piotr-go/DIY-A586/v1.9/3D/panel.png

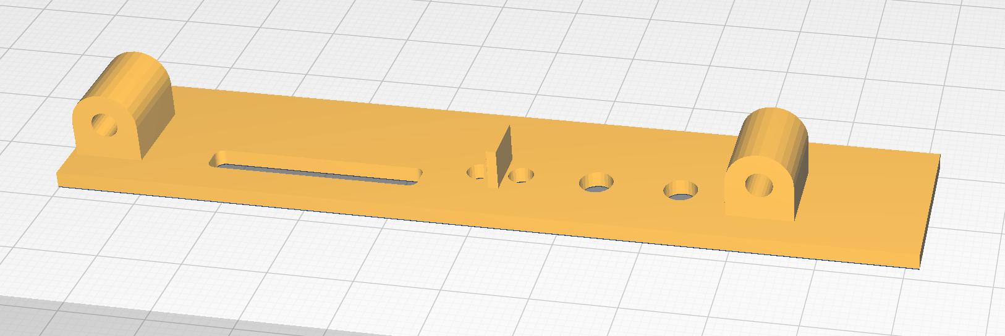
v1.9/3D/panel.png
