piotr-go/DIY-A586/v1.9/cores/amiga/mikan/splitter.png

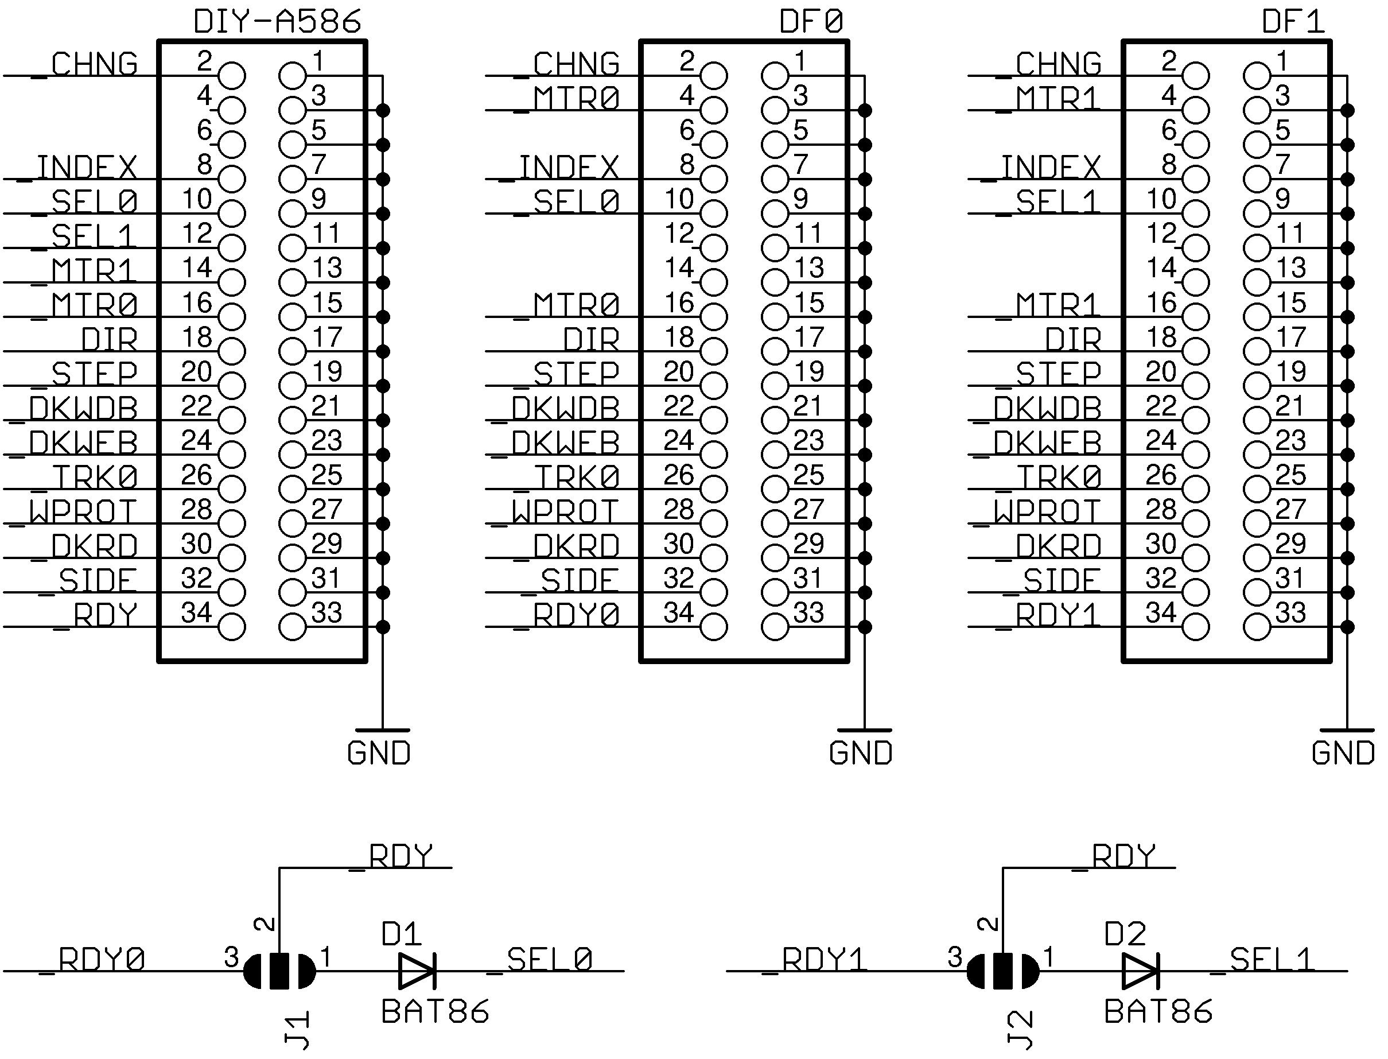
v1.9/cores/amiga/mikan/splitter.png
