piotr-go/DIY-A586/v1.9/pcb/v1.9/bottom.png

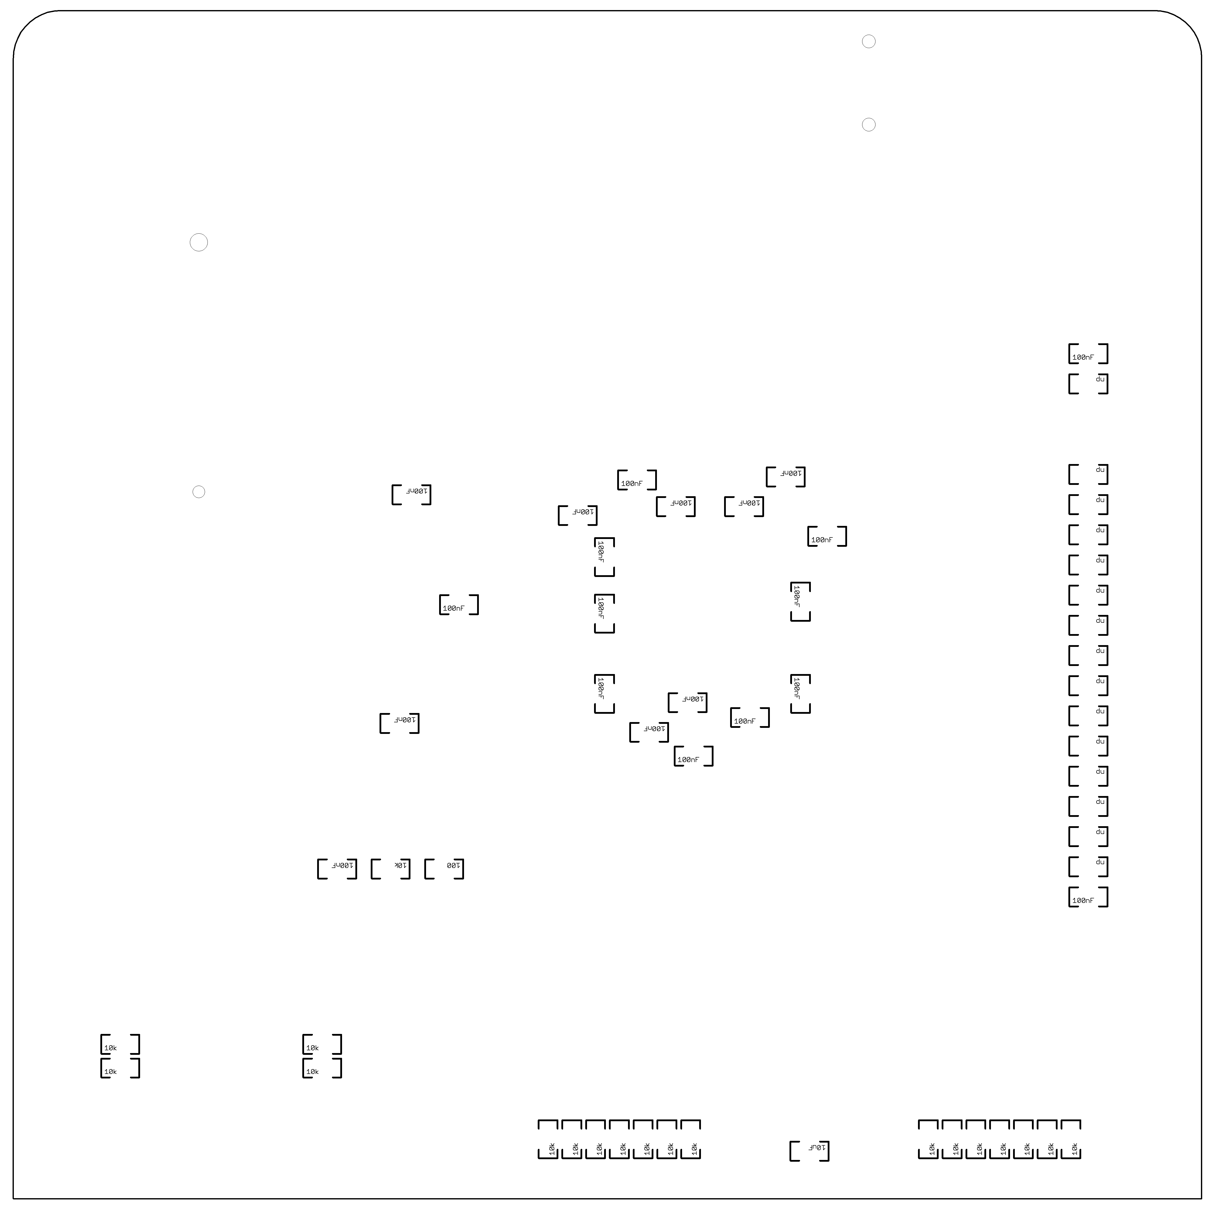
v1.9/pcb/v1.9/bottom.png
