piotr-go/DIY-A586/v1.9/pcb/v1.9/top.png

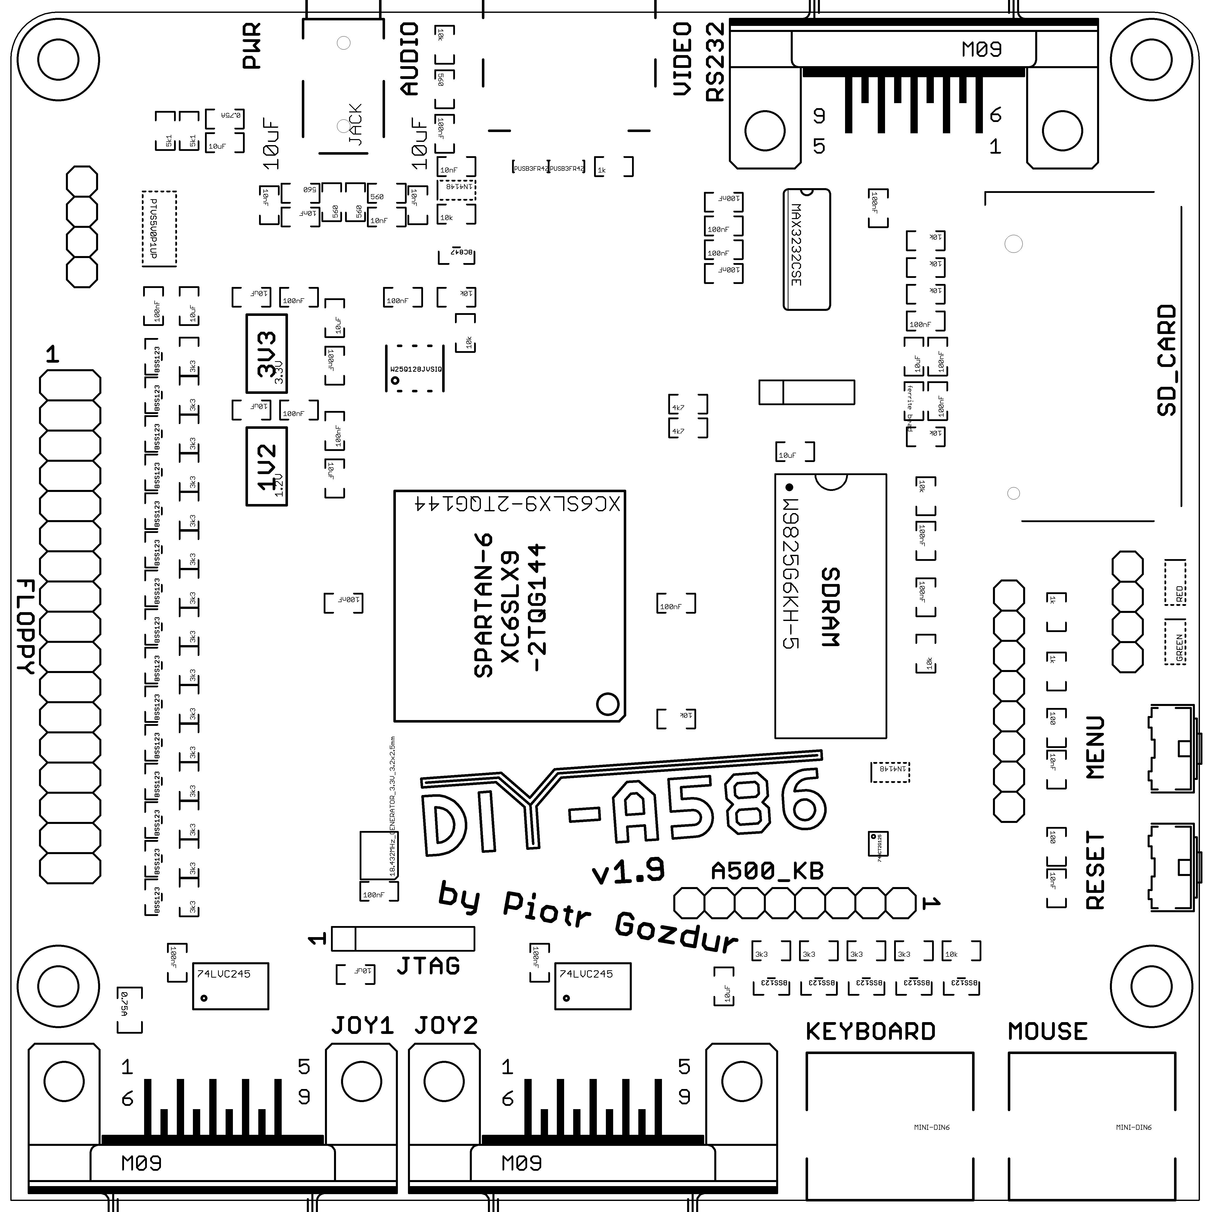
v1.9/pcb/v1.9/top.png
